uvinduuu/AnalogVoltmeter/Images/Enclosure2.jpg

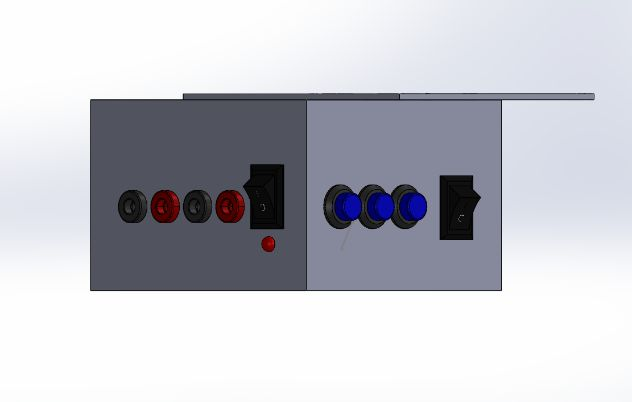
Images/Enclosure2.jpg
