uvinduuu/AnalogVoltmeter/Circuit Design/Draft1.asc

C1: cap; 100µ
C2: cap; 100µ
D1: diode; 1N4148
D2: diode; 1N4148
R1: res; 10k
R2: res; 4.7k
R3: res; 10k
R4: res; 10k
R5: res; 10k
R6: res; 4.7k
R7: res; 2.7k
R8: res; 1k
R9: res; 1k
R10: res; 1k
U1: LM741
U2: LM741
V1: voltage; 20
V2: voltage; SINE(0 6 50)
Named nets: 0
.tran 1
